vives-projectwerk-2-2020/BatteryChargeSystem/DEV boards/Adafruit/projects_fabprint.png

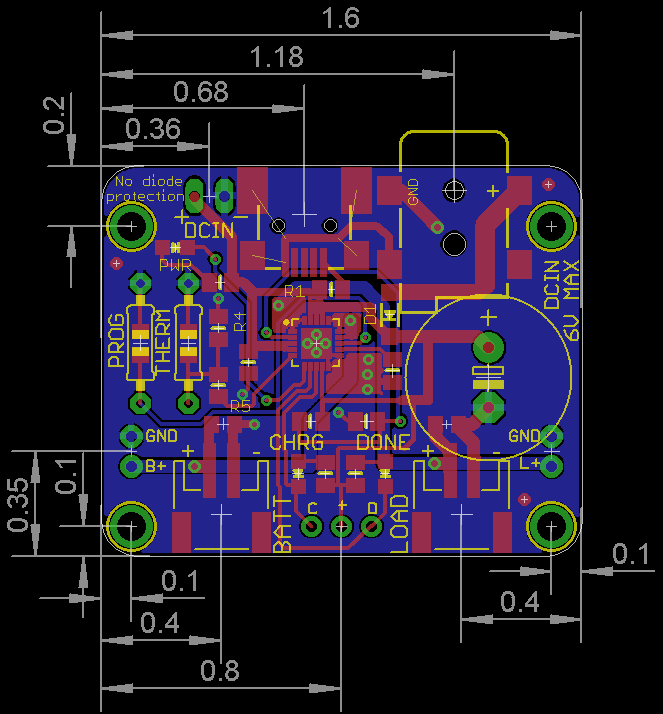
DEV boards/Adafruit/projects_fabprint.png
