vives-projectwerk-2-2020/BatteryChargeSystem/DEV boards/Adafruit/projects_solarv2.png

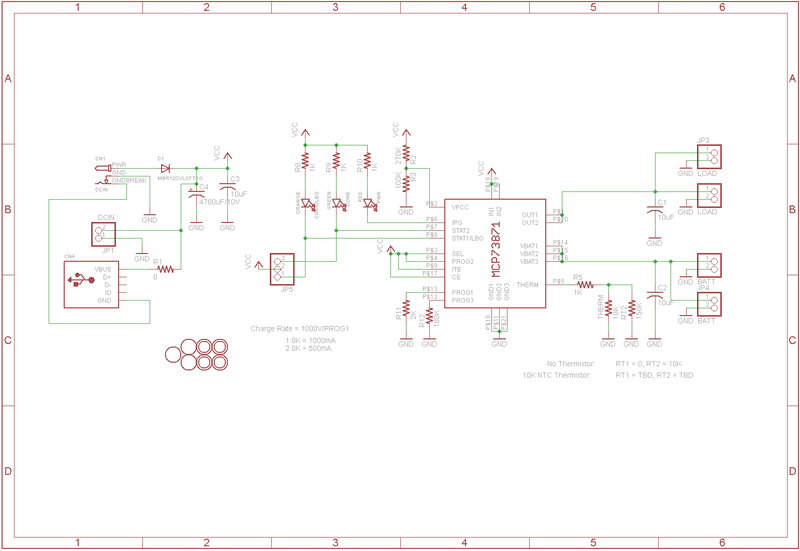
DEV boards/Adafruit/projects_solarv2.png
